bikerglen/music-server-remotes/remote-control/sw/HttpClient.cpp

#include "HttpClient.h"

static const uint16_t TIMEOUT = 5000; // Allow maximum 5s between data packets.

/**
* Constructor.
*/
HttpClient::HttpClient()
{

}

/**
* Method to send a header, should only be called from within the class.
*/
void HttpClient::sendHeader(const char* aHeaderName, const char* aHeaderValue)
{
    client.print(aHeaderName);
    client.print(": ");
    client.println(aHeaderValue);

    #ifdef LOGGING
    Serial.print(aHeaderName);
    Serial.print(": ");
    Serial.println(aHeaderValue);
    #endif
}

void HttpClient::sendHeader(const char* aHeaderName, const int aHeaderValue)
{
    client.print(aHeaderName);
    client.print(": ");
    client.println(aHeaderValue);

    #ifdef LOGGING
    Serial.print(aHeaderName);
    Serial.print(": ");
    Serial.println(aHeaderValue);
    #endif
}

void HttpClient::sendHeader(const char* aHeaderName)
{
    client.println(aHeaderName);

    #ifdef LOGGING
    Serial.println(aHeaderName);
    #endif
}

/**
* Method to send an HTTP Request. Allocate variables in your application code
* in the aResponse struct and set the headers and the options in the aRequest
* struct.
*/
void HttpClient::request(http_request_t &aRequest, http_response_t &aResponse, http_header_t headers[], const char* aHttpMethod)
{
    // If a proper response code isn't received it will be set to -1.
    aResponse.status = -1;
    aResponse.body = "";

    // NOTE: The default port tertiary statement is unpredictable if the request structure is not initialised
    // http_request_t request = {0} or memset(&request, 0, sizeof(http_request_t)) should be used
    // to ensure all fields are zero
    bool connected = false;
    if(aRequest.hostname!=NULL) {
        connected = client.connect(aRequest.hostname.c_str(), (aRequest.port) ? aRequest.port : 80 );
    }   else {
        connected = client.connect(aRequest.ip, aRequest.port);
    }

    #ifdef LOGGING
    if (connected) {
        if(aRequest.hostname!=NULL) {
            Serial.print("HttpClient>\tConnecting to: ");
            Serial.print(aRequest.hostname);
        } else {
            Serial.print("HttpClient>\tConnecting to IP: ");
            Serial.print(aRequest.ip);
        }
        Serial.print(":");
        Serial.println(aRequest.port);
    } else {
        Serial.println("HttpClient>\tConnection failed.");
    }
    #endif

    if (!connected) {
        client.stop();
        // If TCP Client can't connect to host, exit here.
        return;
    }

    //
    // Send HTTP Headers
    //

    // Send initial headers (only HTTP 1.0 is supported for now).
    client.print(aHttpMethod);
    client.print(" ");
    client.print(aRequest.path);
    client.print(" HTTP/1.1\r\n");

    #ifdef LOGGING
    Serial.println("HttpClient>\tStart of HTTP Request.");
    Serial.print(aHttpMethod);
    Serial.print(" ");
    Serial.print(aRequest.path);
    Serial.print(" HTTP/1.1\r\n");
    #endif

    // Send General and Request Headers.
    // sendHeader("Connection", "close"); // Not supporting keep-alive for now.
    if(aRequest.hostname!=NULL) {
        sendHeader("Host", aRequest.hostname.c_str());
    }

    //Send Entity Headers
    // TODO: Check the standard, currently sending Content-Length : 0 for empty
    // POST requests, and no content-length for other types.
    if (headers != NULL)
    {
        int i = 0;
        while (headers[i].header != NULL)
        {
            if (headers[i].value != NULL) {
                sendHeader(headers[i].header, headers[i].value);
            } else {
                sendHeader(headers[i].header);
            }
            i++;
        }
    }

    if (aRequest.body != NULL) {
        sendHeader("Content-Length", (aRequest.body).length());
    } else if (strcmp(aHttpMethod, HTTP_METHOD_POST) == 0) { //Check to see if its a Post method.
        sendHeader("Content-Length", 0);
    }

    // Empty line to finish headers
    client.println();
    client.flush();

    //
    // Send HTTP Request Body
    //

    if (aRequest.body != NULL) {
        client.println(aRequest.body);
        client.flush();

        #ifdef LOGGING
        Serial.println(aRequest.body);
        #endif
    }

    #ifdef LOGGING
    Serial.println("HttpClient>\tEnd of HTTP Request.");
    #endif

    // clear response buffer
    memset(&buffer[0], 0, sizeof(buffer));


    //
    // Receive HTTP Response
    //
    // The first value of client.available() might not represent the
    // whole response, so after the first chunk of data is received instead
    // of terminating the connection there is a delay and another attempt
    // to read data.
    // The loop exits when the connection is closed, or if there is a
    // timeout or an error.

    unsigned int bufferPosition = 0;
    unsigned long lastRead = millis();
    unsigned long firstRead = millis();
    bool error = false;
    bool timeout = false;
    uint16_t actualTimeout = TIMEOUT;
    char lastChar = 0;
    bool inHeaders = true;
    int contentLength = 0;

    do {
        #ifdef LOGGING
        int bytes = client.available();
        if(bytes) {
            Serial.print("\r\nHttpClient>\tReceiving TCP transaction of ");
            Serial.print(bytes);
            Serial.println(" bytes.");
        }
        #endif

        while (client.available()) {
            char c = client.read();
            #ifdef LOGGING
            Serial.print(c);
            #endif
            lastRead = millis();

            if (c == -1) {
                error = true;

                #ifdef LOGGING
                Serial.println("HttpClient>\tError: No data available.");
                #endif

                break;
            }

            if (inHeaders) {
                if ((c == '\n') && (lastChar == '\n')) {
                    // End of headers.  Grab the status code and reset the buffer.
                    aResponse.status = atoi(&buffer[9]);
                    buffer[bufferPosition] = 0;

                    char *clpos = strstr (buffer, "Content-Length: ");
                    if (clpos != NULL) {
                        clpos += 16;
                        contentLength = atoi (clpos);
                        // Serial.printf ("'%s'", clpos);
                        // Serial.printf ("content length is %d\r\n", contentLength);
                    }
                    
                    memset(&buffer[0], 0, sizeof(buffer));
                    bufferPosition = 0;
                    inHeaders = false;
                    
                    #ifdef LOGGING
                    Serial.print("\r\nHttpClient>\tEnd of HTTP Headers (");
                    Serial.print(aResponse.status);
                    Serial.println(")");
                    #endif
                    continue;
                } else if (c != '\r') {
                    lastChar = c;
                }
            }

            // Check that received character fits in buffer before storing.
            if (bufferPosition < sizeof(buffer)-1) {
                buffer[bufferPosition] = c;
            } else if ((bufferPosition == sizeof(buffer)-1)) {
                client.stop();
                error = true;

                #ifdef LOGGING
                Serial.println("\r\nHttpClient>\tError: Response body larger than buffer.");
                #endif
                break;
            }
            bufferPosition++;
            if (bufferPosition == contentLength) {
                client.stop ();
                break;
            }
        }
        // We don't need to null terminate the buffer since it was zeroed to start with, or null terminated when it reached capacity.

        #ifdef LOGGING
        if (bytes) {
            Serial.print("\r\nHttpClient>\tEnd of TCP transaction.");
        }
        #endif

        // Check that there hasn't been more than 5s since last read.
        timeout = millis() - lastRead > actualTimeout;

        // Unless there has been an error or timeout wait 200ms to allow server
        // to respond or close connection.
        if (!error && !timeout) {
            delay(10);
        }
    } while (client.connected() && !timeout && !error);
    
    buffer[bufferPosition] = '\0'; // Null-terminate buffer

    #ifdef LOGGING
    if (timeout) {
        Serial.println("\r\nHttpClient>\tError: Timeout while reading response.");
    }
    Serial.print("\r\nHttpClient>\tEnd of HTTP Response (");
    Serial.print(millis() - firstRead);
    Serial.println("ms).");
    #endif
    client.stop();

    #ifdef LOGGING
    Serial.print("HttpClient>\tStatus Code: ");
    Serial.println(aResponse.status);
    #endif

    if (inHeaders) {
        #ifdef LOGGING
        Serial.println("HttpClient>\tError: Can't find HTTP response body.");
        #endif

        return;
    }
    // Return the entire message body from bodyPos+4 till end.
    aResponse.body = buffer;
}
